EmilNorden/microdrone/controller/src/radio/mod.rs

mod state;

use embassy_embedded_hal::shared_bus::asynch::spi::SpiDevice;
use embassy_sync::blocking_mutex::raw::NoopRawMutex;
use embassy_time::{Delay, Duration, Ticker};
use embedded_hal::digital::OutputPin;
use esp_hal::gpio::{Event, Input, Output};
use esp_hal::spi::master::Spi;
use esp_hal::Async;
use fc_common::{DroneStatus, FlightInput, SignalBase, DRONE_STATUS_SIZE, FLIGHT_INPUT_SIZE};
use nrf24_rs::config::{NrfConfig, PALevel, PayloadSize};
use nrf24_rs::{Nrf24l01, MAX_PAYLOAD_SIZE};
use zerocopy::{FromBytes, IntoBytes};

use crate::moving_sum::MovingSum;
use crate::signal::{
    DroneAltitudeEmitter, DroneBatteryLevelEmitter, InputSignal, RadioEmitter, RadioLinkQualityEmitter, RadioStatus,
};

#[embassy_executor::task]
pub async fn run(
    spi_device: SpiDevice<'static, NoopRawMutex, Spi<'static, Async>, Output<'static>>,
    ce: Output<'static>,
    mut irq: Input<'static>,
    mut input_signal: InputSignal,
    mut radio_status_emitter: RadioEmitter,
    mut drone_altitude_emitter: DroneAltitudeEmitter,
    mut drone_battery_emitter: DroneBatteryLevelEmitter,
    mut radio_link_quality_emitter: RadioLinkQualityEmitter,
) {
    const {
        assert!(
            FLIGHT_INPUT_SIZE < MAX_PAYLOAD_SIZE as usize,
            "FlightInput size exceeds max payload size"
        );
    }
    radio_status_emitter.emit(RadioStatus { connected: false });
    irq.listen(Event::FallingEdge);

    esp_println::println!("TX Radio init");
    let config = NrfConfig::default()
        .channel(76)
        .pa_level(PALevel::Min)
        .payload_size(PayloadSize::Dynamic)
        .ack_payloads_enabled(true);

    let mut delay = Delay;

    let mut radio = match Nrf24l01::new_async(spi_device, ce, &mut delay, config).await {
        Ok(radio) => radio,
        Err(e) => {
            esp_println::println!("NRF24 Error : {:?}", e);
            return;
        }
    };

    if !radio.is_connected().await.unwrap() {
        esp_println::println!("!!! Radio not connected!");
    }
    esp_println::println!("TX Radio connected");
    radio.open_writing_pipe(b"Node1").await.unwrap();

    esp_println::println!("Radio 1 started!");

    let mut ticker = Ticker::every(Duration::from_millis(10));
    let mut i = 0;
    let mut moving_sum: MovingSum<u8, u16, 50> = MovingSum::new();
    let mut quality_update_ticker = 0;
    const QUALITY_UPDATE_FREQUENCY: usize = 10;
    let mut total_failures = 0;
    loop {
        ticker.next().await;
        esp_println::println!("tick! {}   fail: {}", i, total_failures);
        i = i + 1;

        let input: FlightInput = input_signal.get().into();

        match radio.write(&mut delay, input.as_bytes()).await {
            Ok(_) => {
                irq.wait_for_low().await;

                moving_sum.push(radio.retries_in_last_transmission().await.unwrap());
                quality_update_ticker += 1;
                if quality_update_ticker > QUALITY_UPDATE_FREQUENCY {
                    quality_update_ticker = 0;
                    let link_score = 1.0 - (moving_sum.average() / 15.0);
                    radio_link_quality_emitter.emit(link_score);
                }

                let status = radio.status().await.unwrap();
                radio.reset_status().await.unwrap();

                if status.reached_max_retries() {
                    esp_println::println!("MAX_RT");
                    total_failures += 1;
                    radio.flush_tx().await.unwrap();
                } else if let Some(ack) = read_ack(&mut radio).await {
                    radio_status_emitter.emit_if_changed(RadioStatus { connected: true });
                    drone_altitude_emitter.emit(ack.altitude);
                    drone_battery_emitter.emit(ack.battery_level);
                } else {
                    total_failures += 1;
                }
            }
            Err(e) => {
                radio.reset_status().await.unwrap();
                total_failures += 1;
                esp_println::println!("ERR: Radio write error: {:?}", e);
            }
        }
    }
}

async fn read_ack(
    radio: &mut Nrf24l01<
        SpiDevice<'static, NoopRawMutex, Spi<'static, Async>, Output<'static>>,
        Output<'static>,
        nrf24_rs::Async,
    >,
) -> Option<DroneStatus> {
    let mut ack_buffer = [0; 32];
    match radio.read(&mut ack_buffer).await {
        Ok(len) => {
            if len != DRONE_STATUS_SIZE {
                /* After connection has been re-established between controller and drone, it seems like
                there may be ACKs of larger size than expected. I choose to just log these for now */
                esp_println::println!("Received ACK of size {}", len);
                None
            } else {
                if let Ok(drone_status) = DroneStatus::read_from_bytes(&ack_buffer[0..len]) {
                    esp_println::println!("ACK received ({}) {:?}", len, drone_status);
                    Some(drone_status)
                } else {
                    esp_println::println!("Unable to parse ACK");
                    None
                }
            }
        }
        Err(e) => {
            esp_println::println!("Error reading ACK {:?}", e);
            None
        }
    }
}
